ktmizugaki/xiao-75-keyboard/note/adventar2022/switch-sample.jpg

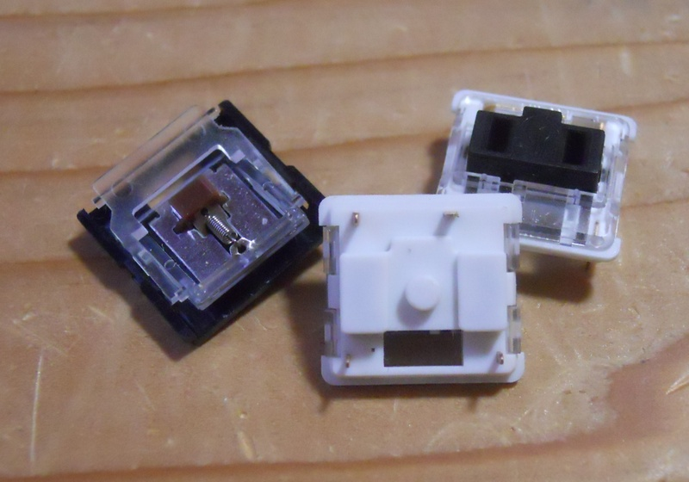
note/adventar2022/switch-sample.jpg
