ktmizugaki/xiao-75-keyboard/note/hackaday/analog-read-circuit.png

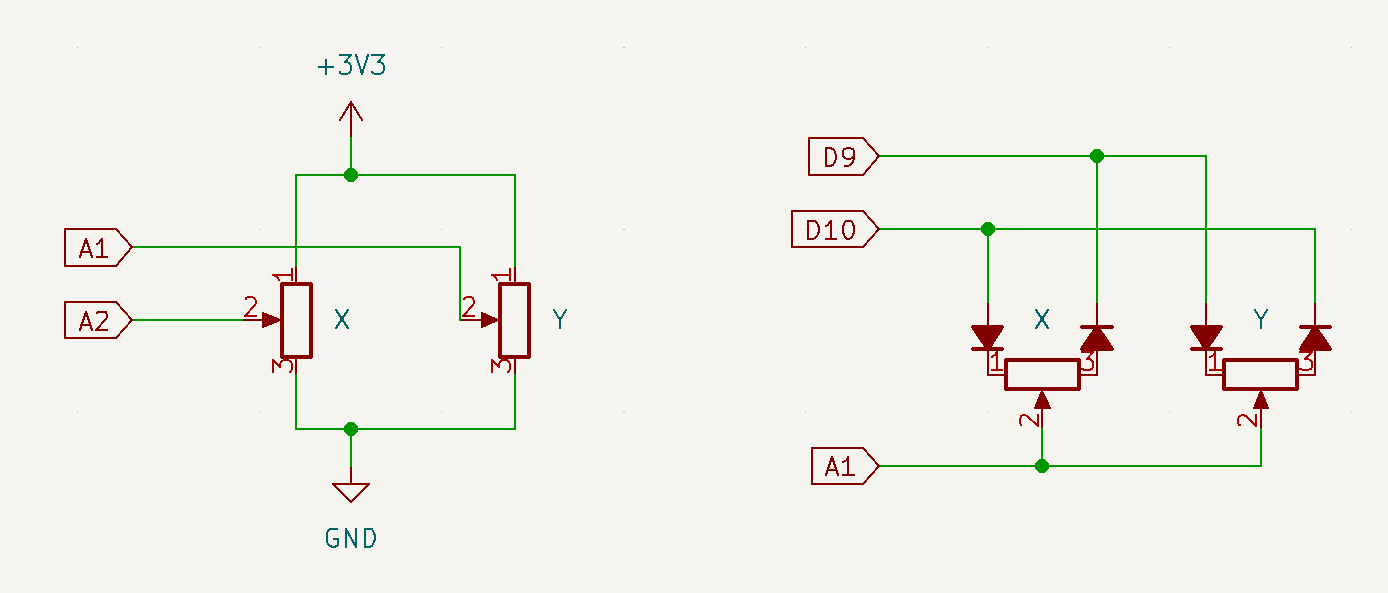
note/hackaday/analog-read-circuit.png
