ktmizugaki/xiao-75-keyboard/note/hackaday/key-switches.jpg

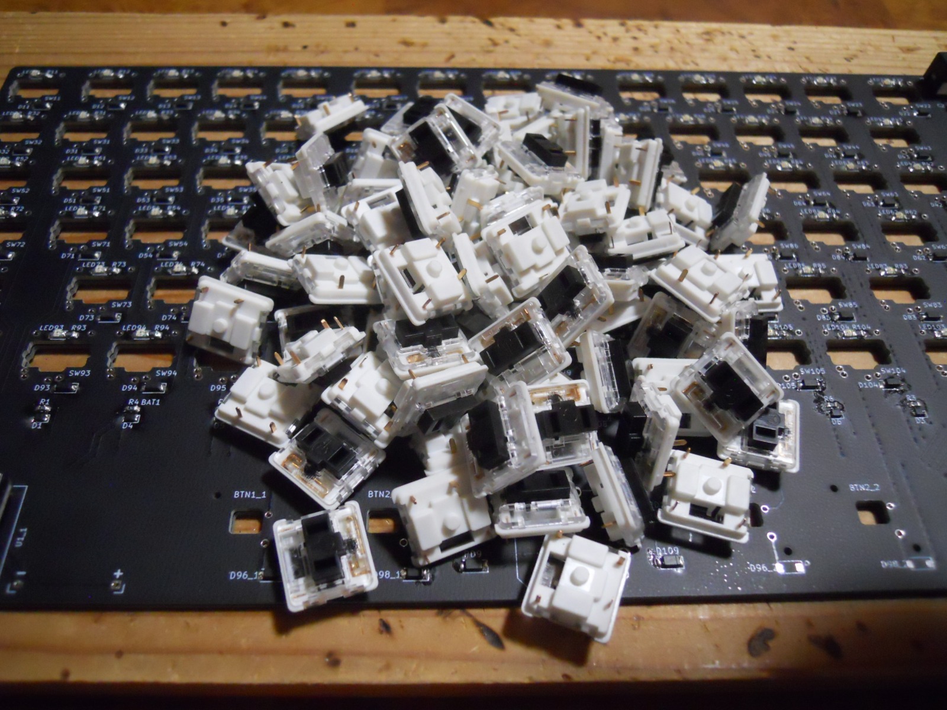
note/hackaday/key-switches.jpg
