ktmizugaki/xiao-75-keyboard/note/hackaday/keycap-second-sketch.png

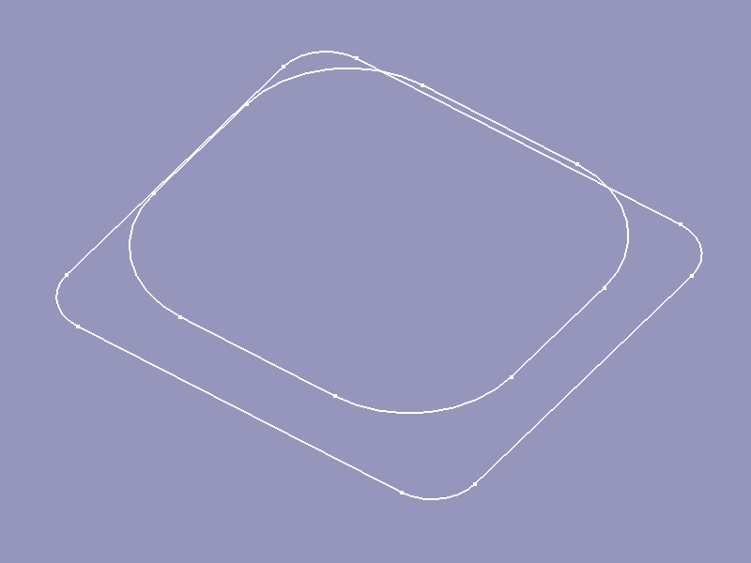
note/hackaday/keycap-second-sketch.png
