ktmizugaki/xiao-75-keyboard/note/hackaday/xiao-75-keyboard-3d.jpg

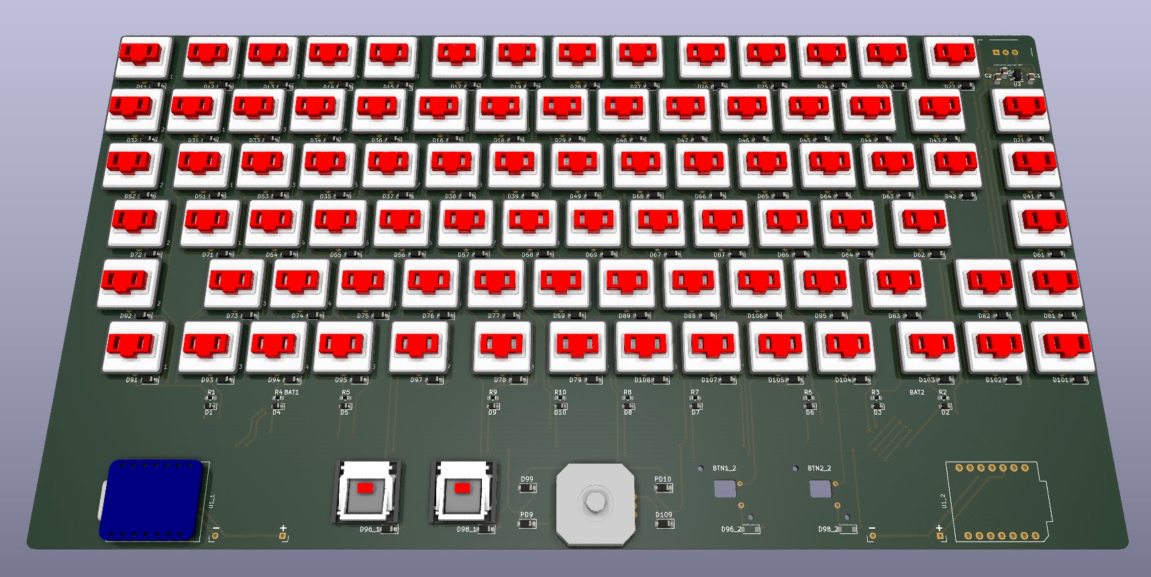
note/hackaday/xiao-75-keyboard-3d.jpg
