ktmizugaki/xiao-75-keyboard/note/hackaday/xiao-75-keyboard-on-netbook.jpg

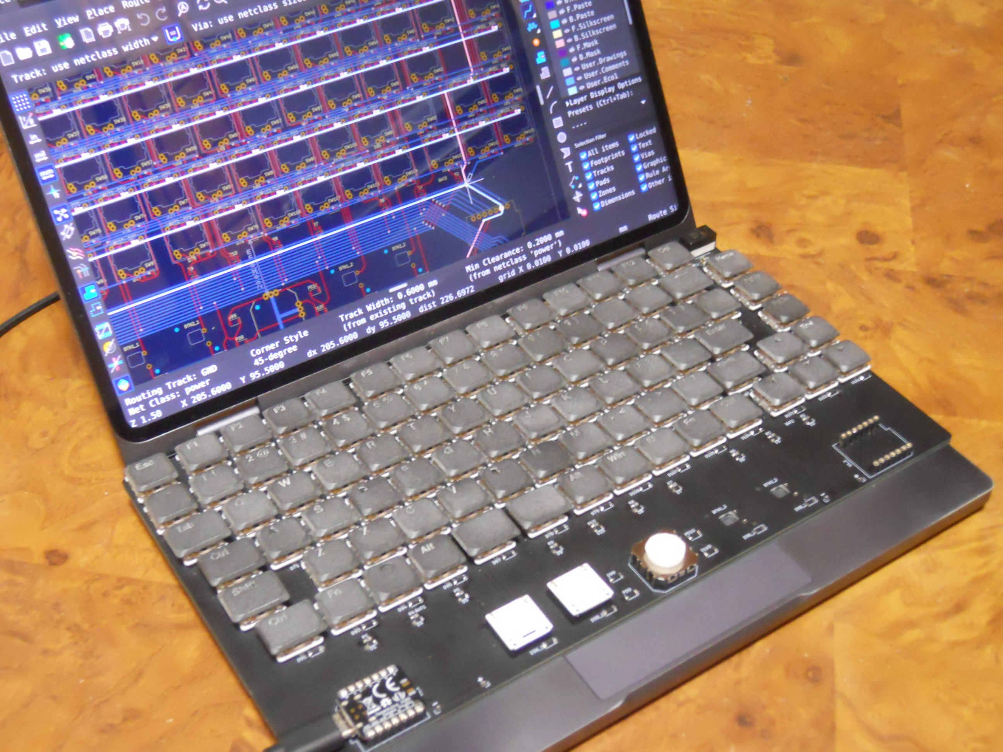
note/hackaday/xiao-75-keyboard-on-netbook.jpg
