ktmizugaki/xiao-75-keyboard/note/hackaday/xiao-75-keyboard-pcb.jpg

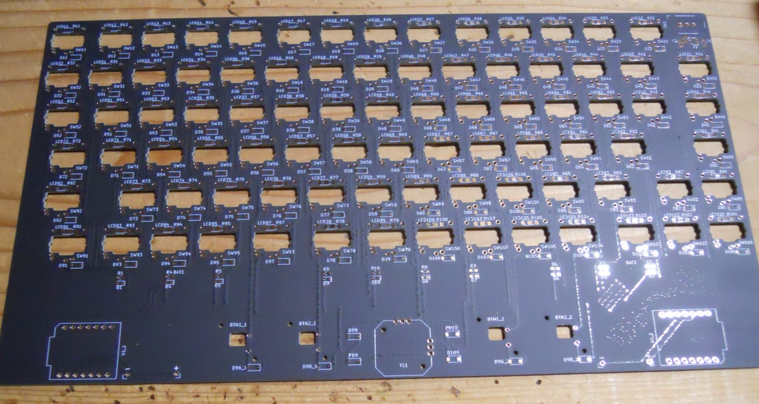
note/hackaday/xiao-75-keyboard-pcb.jpg
