ktmizugaki/xiao-75-keyboard/note/hackaday/xiao-75-keyboard-top-view.jpg

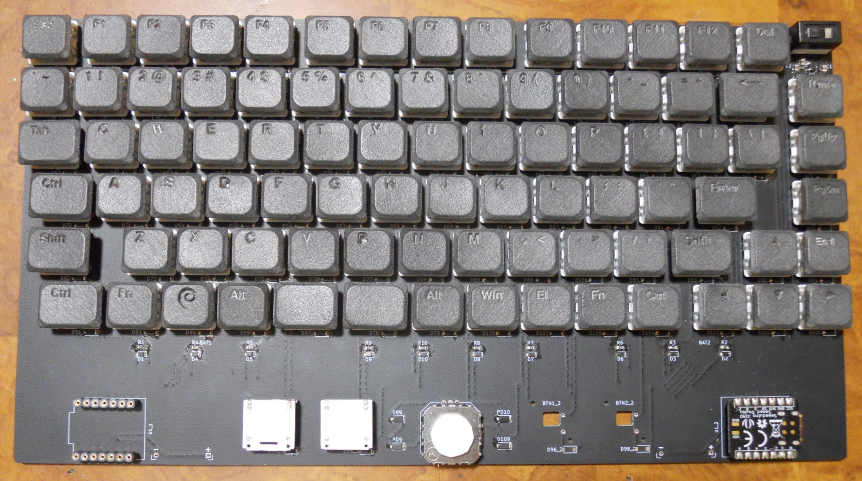
note/hackaday/xiao-75-keyboard-top-view.jpg
