ktmizugaki/xiao-75-keyboard/resources/analog-diode.png

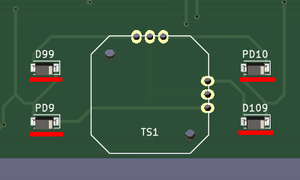
resources/analog-diode.png
