ktmizugaki/xiao-75-keyboard/resources/analog-stick.png

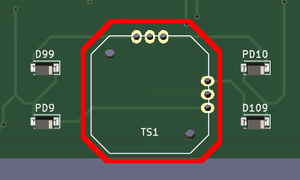
resources/analog-stick.png
