ktmizugaki/xiao-75-keyboard/resources/bl-power.png

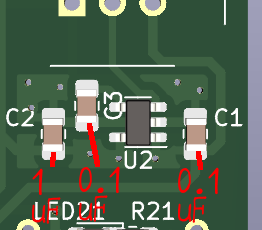
resources/bl-power.png
