ktmizugaki/xiao-75-keyboard/resources/button-diode.png

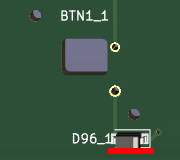
resources/button-diode.png
