ktmizugaki/xiao-75-keyboard/resources/led-sample.jpg

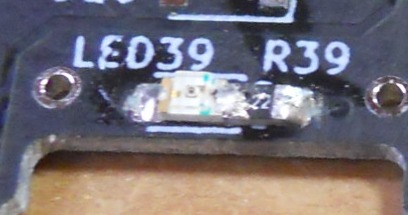
resources/led-sample.jpg
