ktmizugaki/xiao-75-keyboard/resources/xiao-75-keyboard-3d-pcb-small.png

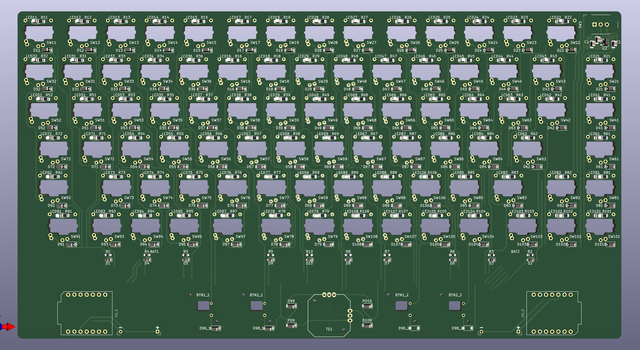
resources/xiao-75-keyboard-3d-pcb-small.png
